impatrq/asyst/Documentacion/Celda-de-carga/Celda.png

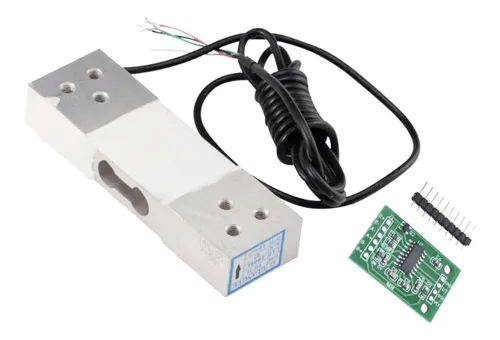
Documentacion/Celda-de-carga/Celda.png
