impatrq/asyst/Documentacion/Celda-de-carga/Modelo 3D celda.png

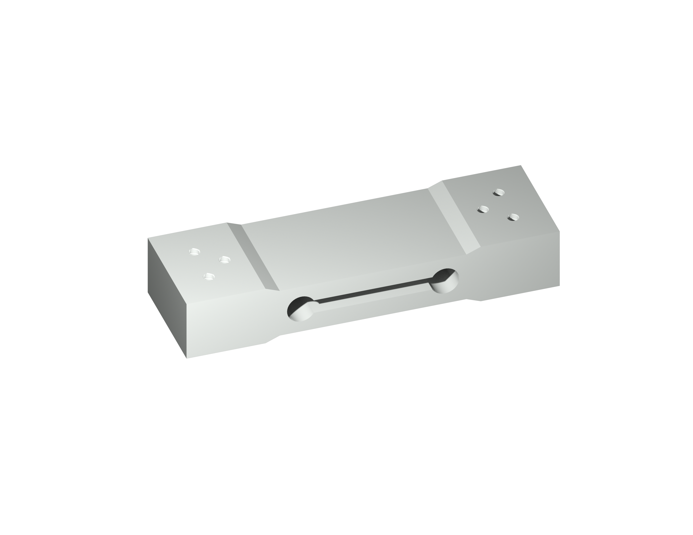
Documentacion/Celda-de-carga/Modelo 3D celda.png
