impatrq/asyst/Documentacion/Display/Display_frente.webp

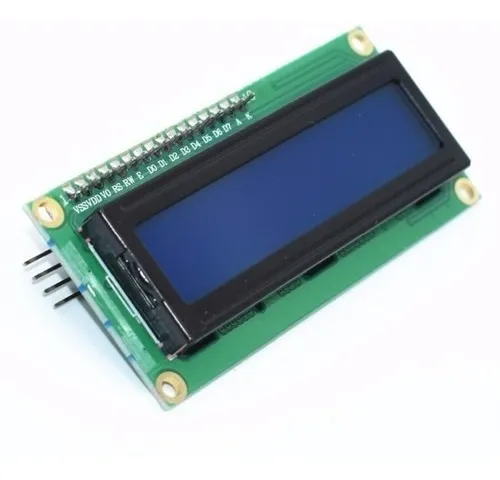
Documentacion/Display/Display_frente.webp
