impatrq/asyst/Documentacion/Display/Display_trasero.webp

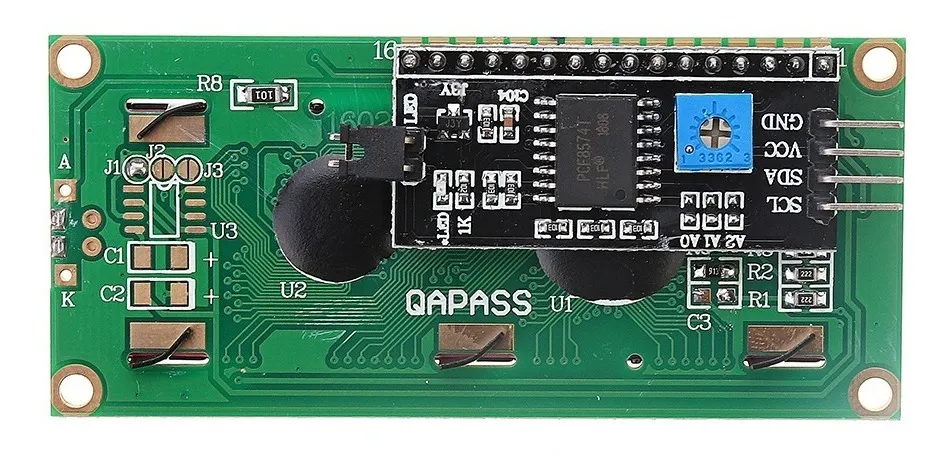
Documentacion/Display/Display_trasero.webp
